Athwale/Archery-clock/V2-rev1/Hardware/burner/PDF/burner-B_Cu.pdf

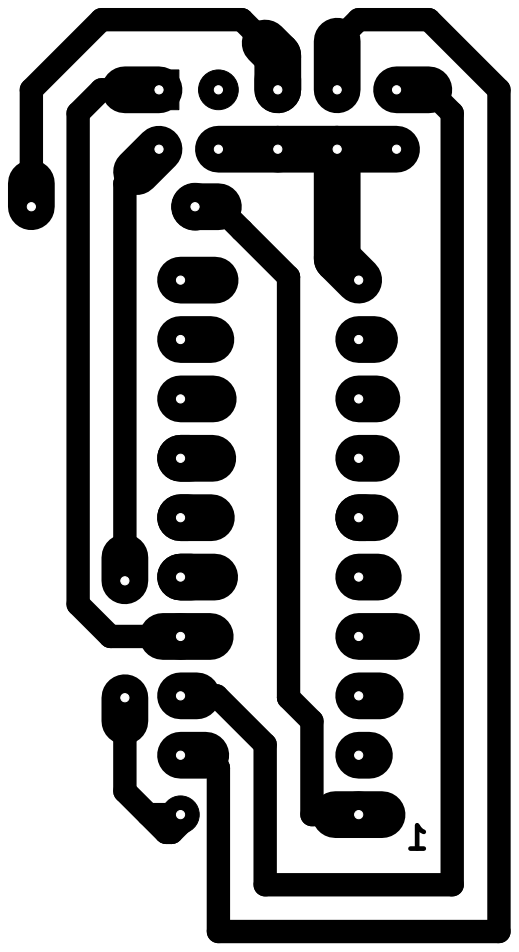
[picture p24: page 1]
