Athwale/Archery-clock/V2-rev1/Hardware/burner/PDF/burner-B_Mask.pdf

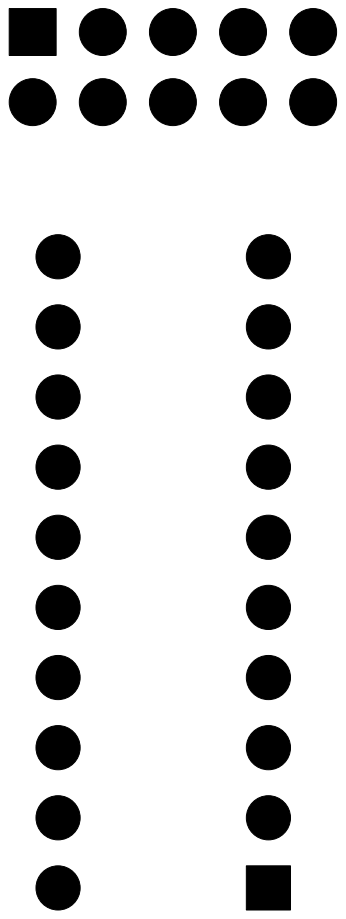
[picture p25: page 1]
