Athwale/Archery-clock/V2-rev1/Hardware/burner/PDF/burner-Eco2_User.pdf

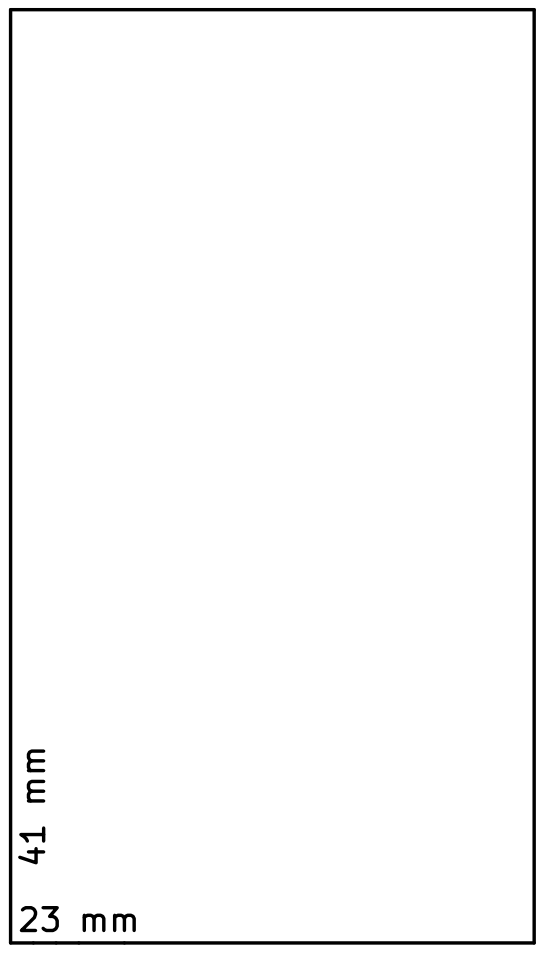
[picture p26: page 1]
