Athwale/Archery-clock/V2-rev1/Hardware/controller/PDF/controller-B_Cu.pdf

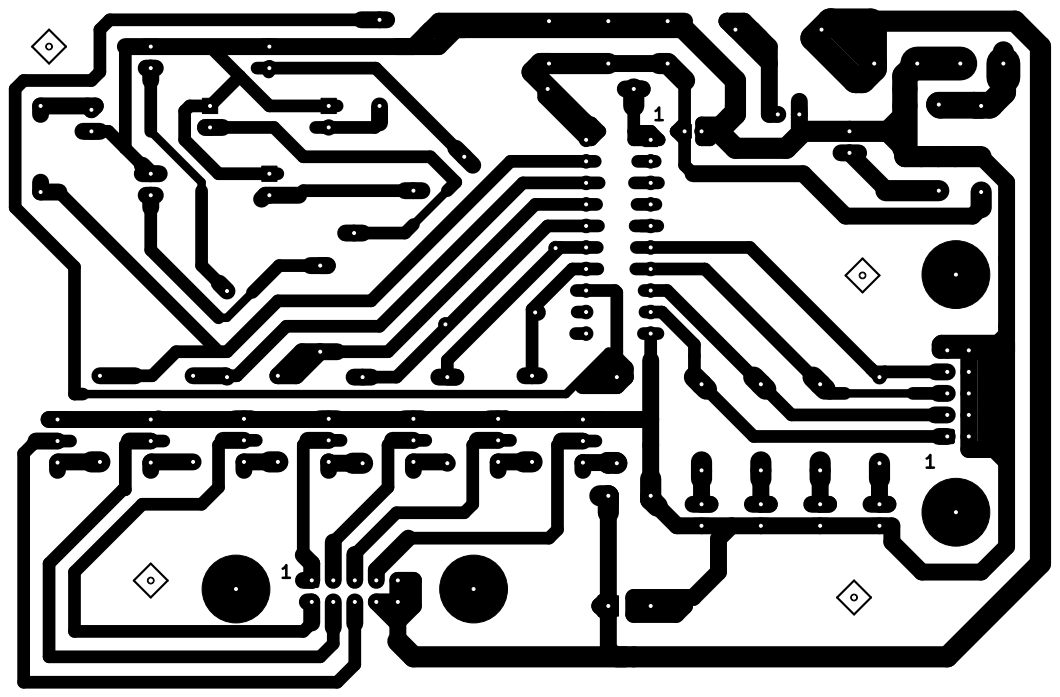
[picture p27: page 1]
