Athwale/Archery-clock/V2-rev1/Hardware/controller/PDF/controller-B_Mask.pdf

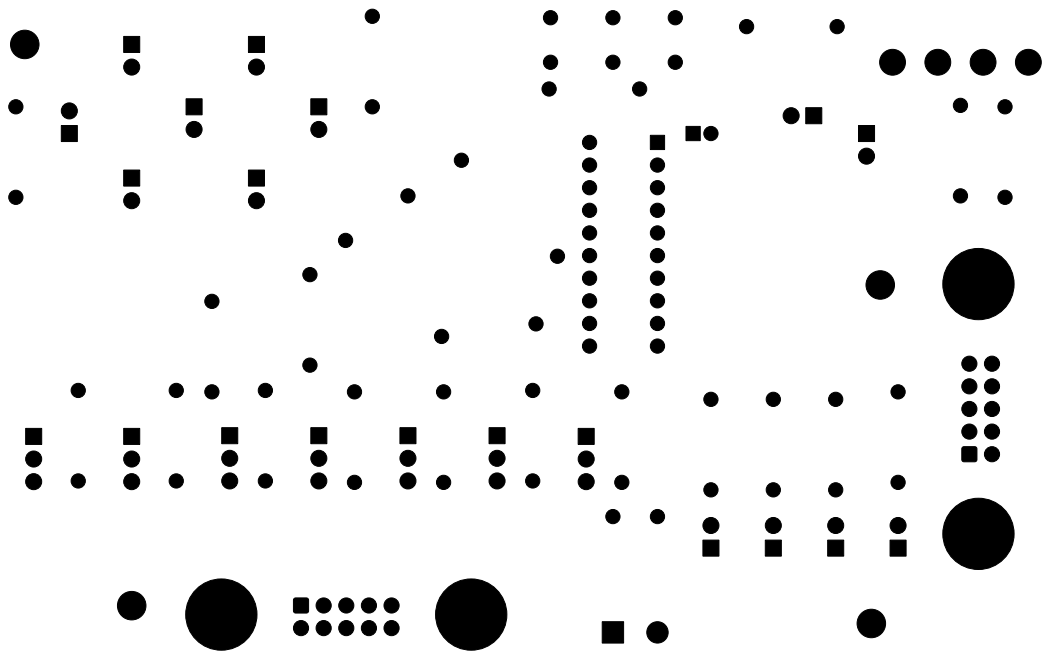
[picture p28: page 1]
