Athwale/Archery-clock/V2-rev1/Hardware/controller/PDF/controller-Eco2_User.pdf

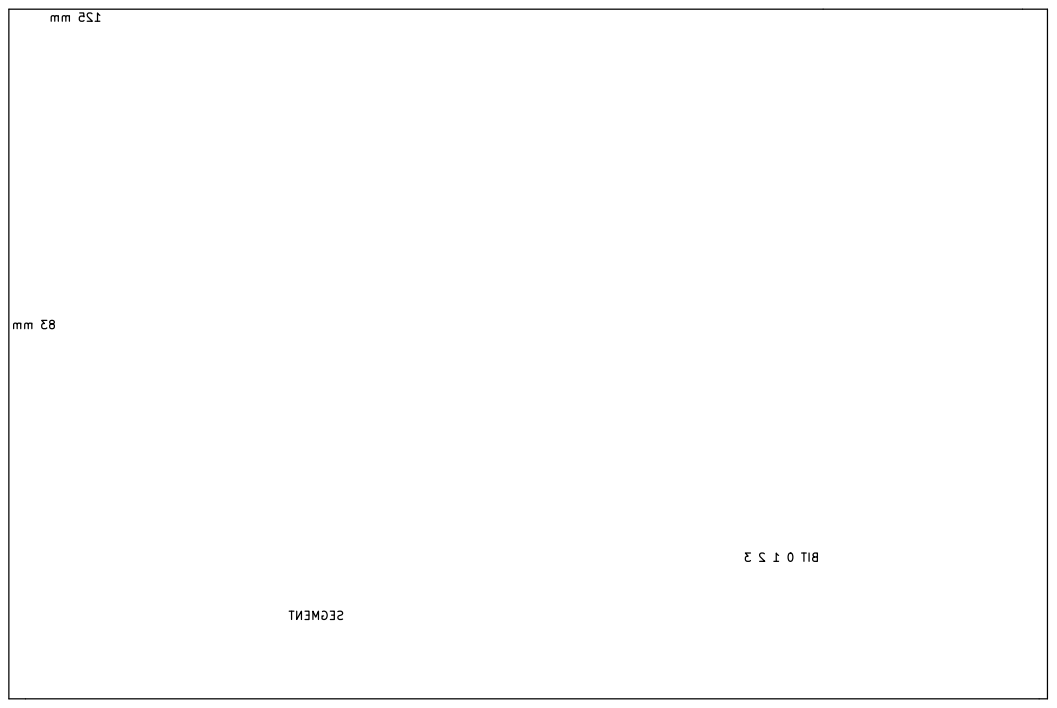
[picture p29: page 1]
