Athwale/Archery-clock/V2-rev1/Hardware/splitter/PDF/splitter-B_Cu.pdf

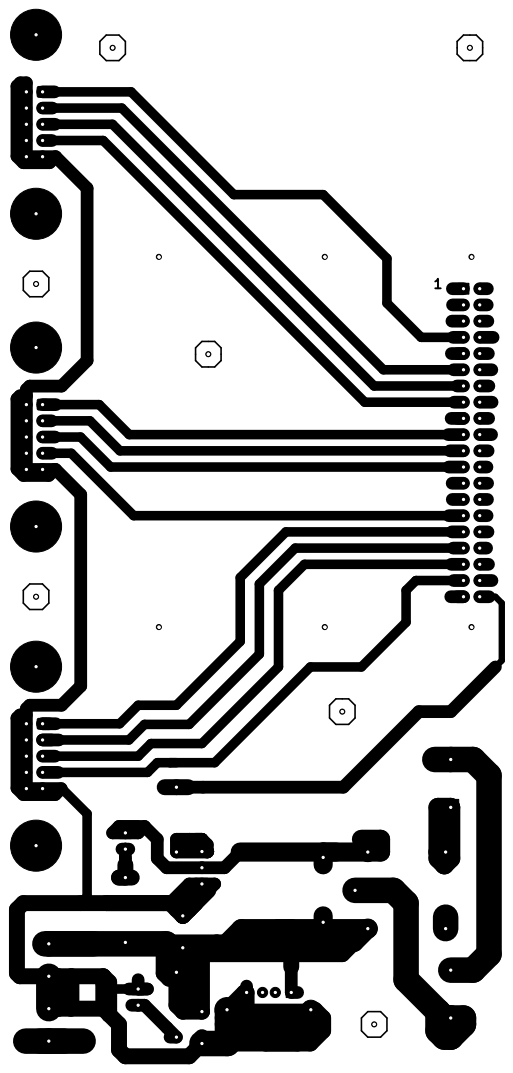
[picture p30: page 1]
