Athwale/Archery-clock/V2-rev1/Hardware/splitter/PDF/splitter-B_Mask.pdf

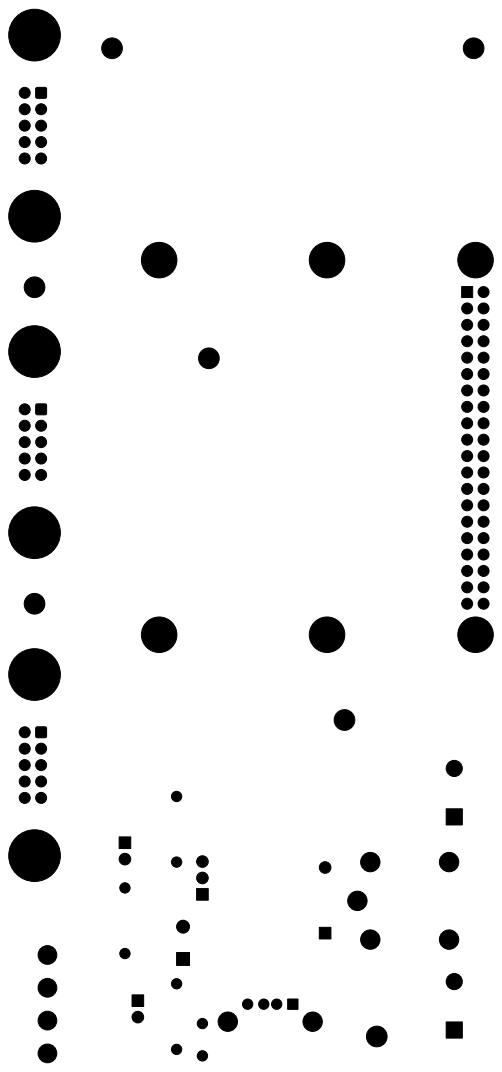
[picture p31: page 1]
