Athwale/Archery-clock/V2-rev1/Hardware/splitter/PDF/splitter-Eco2_User.pdf

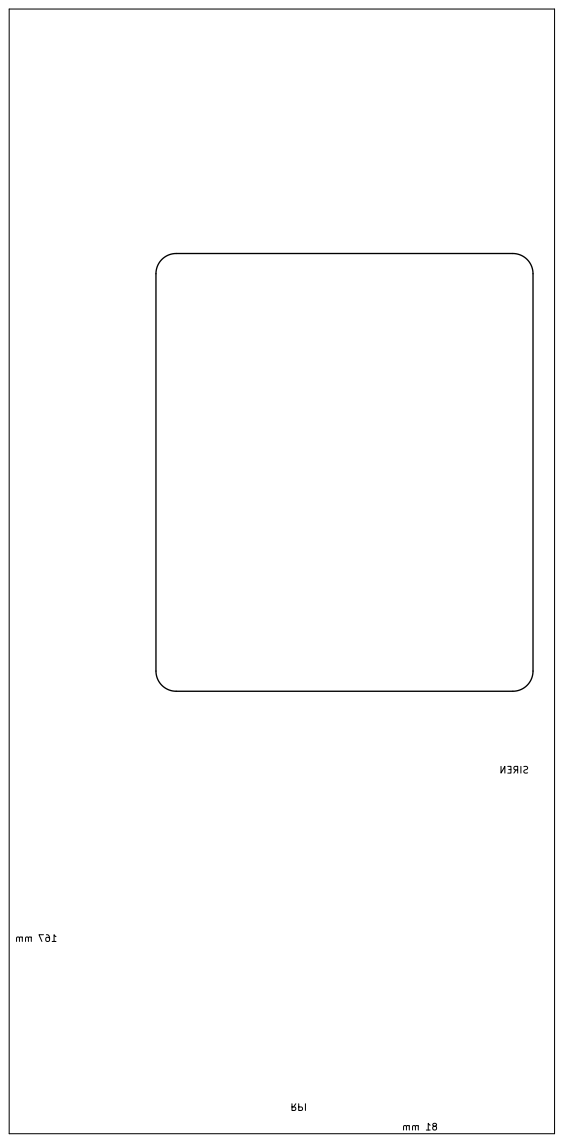
[picture p32: page 1]
