Athwale/Archery-clock/V2/archery.sch

## KiCad design V2/archery.sch (2020-04-22)

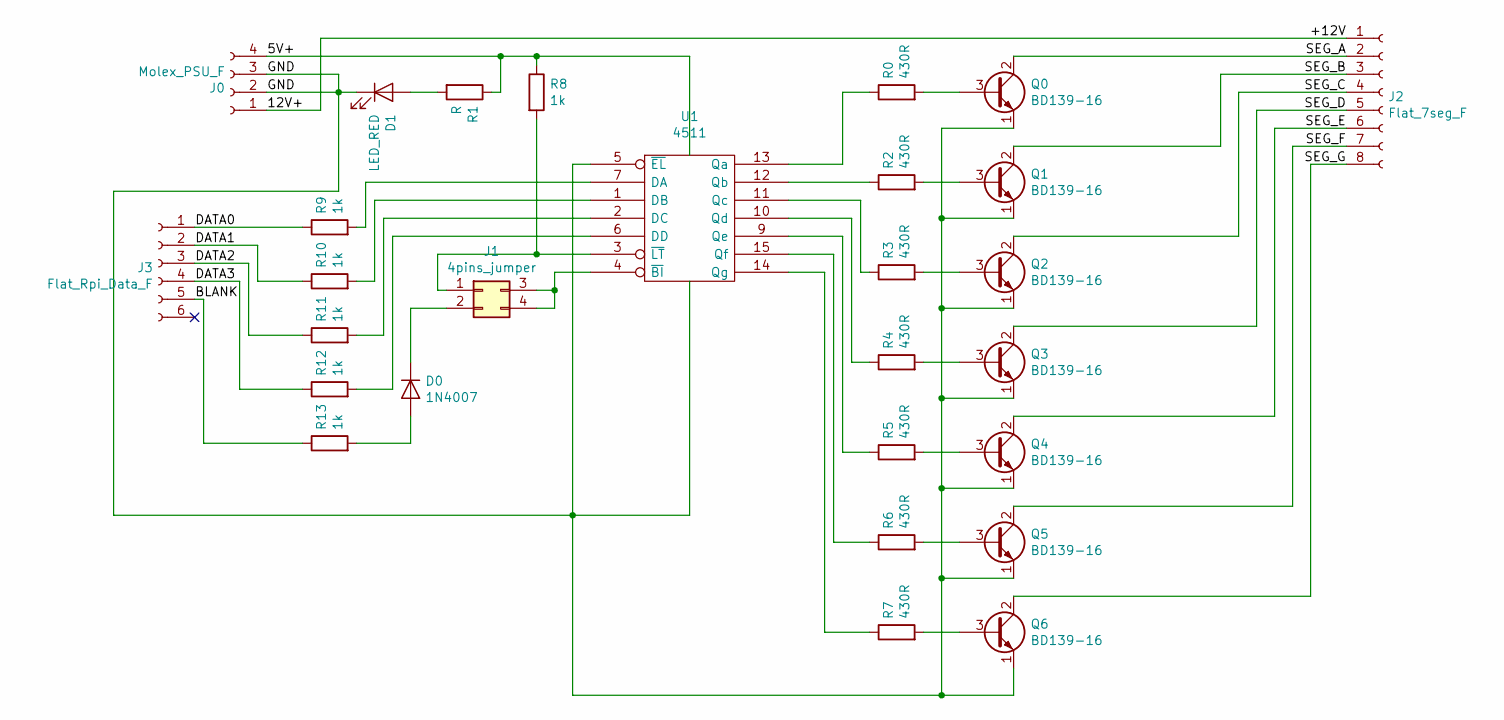
[picture p39: schematic archery.sch]

Parts:
D0: 1N4007
D1: LED_RED
J0: Molex_PSU_F
J1: 4pins_jumper
J2: Flat_7seg_F
J3: Flat_Rpi_Data_F
Q0, Q1, Q2, Q3, Q4, Q5, Q6: BD139-16
R0, R2, R3, R4, R5, R6, R7: 430R
R1: R
R8, R9, R10, R11, R12, R13: 1k
U1: 4511

Connections:
5V+: J0.4, R1.1, R8.1, U1.16 (Vdd)
+12V: J0.1, J2.1
BLANK: J3.5, R13.1
DATA0: J3.1, R9.1
DATA1: J3.2, R10.1
DATA2: J3.3, R11.1
DATA3: J3.4, R12.1
GND: D1.1 (K), J0.2, J0.3, Q0.1 (E), Q1.1 (E), Q2.1 (E), Q3.1 (E), Q4.1 (E), Q5.1 (E), Q6.1 (E), U1.5 (~EL), U1.8 (Vss)
unnamed: D0.1 (K), J1.2
unnamed: D0.2 (A), R13.2
unnamed: D1.2 (A), R1.2
unnamed: J1.1, R8.2, U1.3 (~LT)
unnamed: J1.3, J1.4, U1.4 (~BI)
unnamed: Q0.3 (B), R0.2
unnamed: Q1.3 (B), R2.2
unnamed: Q2.3 (B), R3.2
unnamed: Q3.3 (B), R4.2
unnamed: Q4.3 (B), R5.2
unnamed: Q5.3 (B), R6.2
unnamed: Q6.3 (B), R7.2
unnamed: R0.1, U1.13 (Qa)
unnamed: R2.1, U1.12 (Qb)
unnamed: R3.1, U1.11 (Qc)
unnamed: R4.1, U1.10 (Qd)
unnamed: R5.1, U1.9 (Qe)
unnamed: R6.1, U1.15 (Qf)
unnamed: R7.1, U1.14 (Qg)
unnamed: R9.2, U1.7 (DA)
unnamed: R10.2, U1.1 (DB)
unnamed: R11.2, U1.2 (DC)
unnamed: R12.2, U1.6 (DD)
SEG_A: J2.2, Q0.2 (C)
SEG_B: J2.3, Q1.2 (C)
SEG_C: J2.4, Q2.2 (C)
SEG_D: J2.5, Q3.2 (C)
SEG_E: J2.6, Q4.2 (C)
SEG_F: J2.7, Q5.2 (C)
SEG_G: J2.8, Q6.2 (C)
